hazenluk/RP2040_AS3394/spice files/twin_t_test.asc

C1: cap; 10n
C2: cap; 2.65258238n
C3: cap; 2.65258238n
C4: cap; 5.30516477n
R1: res; 15.9K
R2: res; 15.9K
R3: res; 2000
R4: res; 2000
R5: res; 1000
U1: LM741
V1: voltage; 6.5
V2: voltage; -6.5
V3: voltage; ""; AC 1
Named nets: 0, 6.5V, -6.5V
.ac dec 20 1 1000000
.param duty = 0.5
