hazenluk/RP2040_AS3394/spice files/VCO.asc

C1: cap; 10n
C2: cap; 33n
C3: cap; 10n
C4: cap; 180n
R1: res; 6.8k
R2: res; 11k
R3: res; 6.8k
R4: res; 5.1k
R5: res; 2.7k
R6: res; 3.3k
R7: res; 3.9k
R8: res; 1k
U1: LM324
U2: LM324
V1: voltage; 6.5V
V2: voltage; -6.5V
V3: voltage; PULSE(0 3.3 0 0.0000001 0.0000001 {duty*0.000032768} 0.000032768 150); AC 1
V4: voltage; 1.0198854
V5: voltage; 5
Named nets: 0, -6.5V, in, out, 6.5V
.tran .01
.param duty = 0.5
