hazenluk/RP2040_AS3394/spice files/Mixer.asc

C1: cap; 22µ
C2: cap; .047µ
R1: res; 1k
R2: res; 1.5k
R3: res; 4.3k
R4: res; 100
U1: LM324
V1: voltage; 6.5V
V2: voltage; -6.5V
V3: voltage; PULSE(0 3.3 0 0.0000001 0.0000001 {duty*0.000032768} 0.000032768 15000); AC 1
Named nets: 0, -6.5V, in, out, 6.5V
.tran .3
.param duty = 0.01
