hazenluk/RP2040_AS3394/spice files/Mod_Amt.asc

C1: cap; 10n
C2: cap; 15n
C3: cap; .047µ
R1: res; 12k
R2: res; 15k
R3: res; 510
R4: res; 2.4k
R5: res; 120
U1: LM324
V1: voltage; 6.5V
V2: voltage; -6.5V
V3: voltage; PULSE(0 3.3 0 0.0000001 0.0000001 {duty*0.000032768} 0.000032768 150); AC 1
Named nets: 0, -6.5V, in, 6.5V, out
.tran .005
.param duty = 0.5
