hazenluk/RP2040_AS3394/spice files/Pulse_Width_PWM.asc

C1: cap; 56n
R1: res; 2.7k
R2: res; 6.2k
V1: voltage; 6.5V
V2: voltage; -6.5V
V3: voltage; 3.3; AC 1
Named nets: 0, -6.5V, in, 6.5V, out
.ac dec 20 1 1000000
