hazenluk/RP2040_AS3394/spice files/Wave_Select.asc

R1: res; 2k
R2: res; 2k
R3: res; 1k
R4: res; 2k
R5: res; 9.1k
R6: res; 18k
R7: res; 33k
U1: LM324_ST
V1: voltage; 3.3
V2: voltage; 0
V3: voltage; -6.5
V4: voltage; 6.5
V5: voltage; -6.5
Named nets: 0, vout
.op
